alvarop/chaac/fw/chaac/src/app/usb_lora/app_main.c

#include <stdbool.h>
#include "stm32l4xx_hal.h"
#include "FreeRTOS.h"
#include "task.h"
#include "main.h"
#include "printf.h"
#include "debug.h"
#include "gpio.h"
#include "usb_device.h"
#include "chaac_packet.h"
#include "packet.h"
#include "vcp.h"
#include "loraRadio.h"
#include "spi.h"
#include "memfault/components.h"
#include "memfault/core/data_packetizer.h"
#include "usb_dfu.h"
#include "info.h"

#define BUFFER_SIZE 300

static uint8_t txbuff[BUFFER_SIZE];

void vcpPacketTxFn(uint16_t len, void* data) {
    vcpTx(data, len);
}

void radioPacketTxFn(uint16_t len, void* data) {
    loraRadioSend(data, len);
}


loraMode_t loraRxCallback(uint8_t *buff, size_t len, int16_t rssi, int8_t snr){

    // Check packet CRC
    if(packetIsValid(buff, len) && (len <= BUFFER_SIZE)) {
        packet_header_t *header = (packet_header_t *)buff;

        memcpy(txbuff, (void *)&header[1], header->len);

        chaac_lora_rxinfo_t *footer = (chaac_lora_rxinfo_t *)&txbuff[len];
        footer->rssi = rssi;
        footer->snr = snr;

        packetTx(len + sizeof(chaac_lora_rxinfo_t), txbuff, vcpPacketTxFn);
    }

    HAL_GPIO_WritePin(LED1_GPIO_Port, LED1_Pin, GPIO_PIN_SET);
    vTaskDelay(50);
    HAL_GPIO_WritePin(LED1_GPIO_Port, LED1_Pin, GPIO_PIN_RESET);

    return RADIO_MODE_RX;
}

loraMode_t loraTxCallback() {
    return RADIO_MODE_RX;
}

loraMode_t loraRxTimeoutCallback() {
    return RADIO_MODE_RX;
}

loraMode_t loraTxTimeoutCallback() {
    return RADIO_MODE_RX;
}

loraMode_t loraRxErrorCallback() {
    return RADIO_MODE_RX;
}

typedef enum {
    usbCmdReboot = 0,
    usbCmdBootloader = 1,
    getMemfaultData = 2,
    usbCmdPing = 3,
    usbCmdPong = 4,
} chaacUSBCommand_t;

#define MEMFAULT_DATA_MAX_LEN 256
static void sendMemfaultData() {
    uint8_t *buf = pvPortMalloc(MEMFAULT_DATA_MAX_LEN);
    memfault_packet_t *packet = (memfault_packet_t *)buf;
    packet->header.uid = getHWID();
    packet->header.type = PACKET_TYPE_MEMFAULT;
    size_t buf_len = MEMFAULT_DATA_MAX_LEN - sizeof(memfault_packet_t);
    if(memfault_packetizer_get_chunk(&packet[1], &buf_len)) {
        packet->len = buf_len;
        packetTx(buf_len + sizeof(memfault_packet_t), buf, vcpPacketTxFn);
    }
    vPortFree(buf);
}

void processUSBCommand(usb_cmd_packet_t *packet) {
    switch(packet->cmd) {
        case usbCmdReboot: {
            NVIC_SystemReset();
            break;
        }

        case usbCmdBootloader: {
            dfuReset();
            break;
        }
        
        case getMemfaultData: {
            sendMemfaultData();
            break;
        }

        case usbCmdPing: {
            usb_cmd_packet_t response;
            response.header.uid = 0;
            response.header.type = PACKET_TYPE_USB_CMD;
            response.cmd = usbCmdPong;
            response.len = 0;
            packetTx(sizeof(usb_cmd_packet_t), &response, vcpPacketTxFn);
            break;
        }

        default: {
            break;
        }
    }
}

void packetRxFn(uint16_t len, void* data) {
    do {
        if (len < sizeof(chaac_header_t)) {
            break;
        }

        usb_cmd_packet_t *packet = (usb_cmd_packet_t *)data;
        if(packet->header.uid == 0 && packet->header.type == PACKET_TYPE_USB_CMD) {
            processUSBCommand(packet);
            break;
        }

        HAL_GPIO_WritePin(LED1_GPIO_Port, LED1_Pin, GPIO_PIN_SET);
        packetTx(len, data, radioPacketTxFn);
        HAL_GPIO_WritePin(LED1_GPIO_Port, LED1_Pin, GPIO_PIN_RESET);
    }
    while(0);
}

static loraRadioConfig_t loraConfig = {
    .startMode = RADIO_MODE_RX,
    .spiSetupFn = NULL,
    .spiTeardownFn = NULL,
    .rxCb = loraRxCallback,
    .txCb = loraTxCallback,
    .rxTimeoutCb = loraRxTimeoutCallback,
    .txTimeoutCb = loraTxTimeoutCallback,
    .rxErrorCb = loraRxErrorCallback,
};

int main(void) {
    
    dfuCheck();

    HAL_Init();

    SystemClock_Config();

    MX_GPIO_Init();
    MX_USB_DEVICE_Init();
    MX_SPI1_Init();

    memfault_platform_boot();

    packetInitCb(packetRxFn);

    vcpInit();
    vcpSetRxByteCallback(packetProcessByte);

    loraRadioInit(&loraConfig);

    vTaskStartScheduler();

    __builtin_unreachable();
}
